sagdusmir/G32-Grill-Display-320x172-BT/misc/assembly/assembly_3_slide_pololu_down_the_case.jpeg

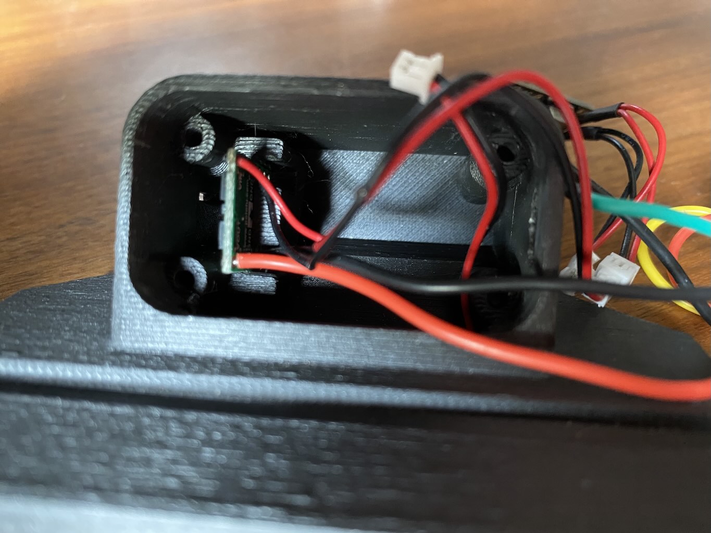
misc/assembly/assembly_3_slide_pololu_down_the_case.jpeg
