sagdusmir/G32-Grill-Display-320x172-BT/misc/assembly/assembly_4_orientation_of_the_charger_board.jpeg

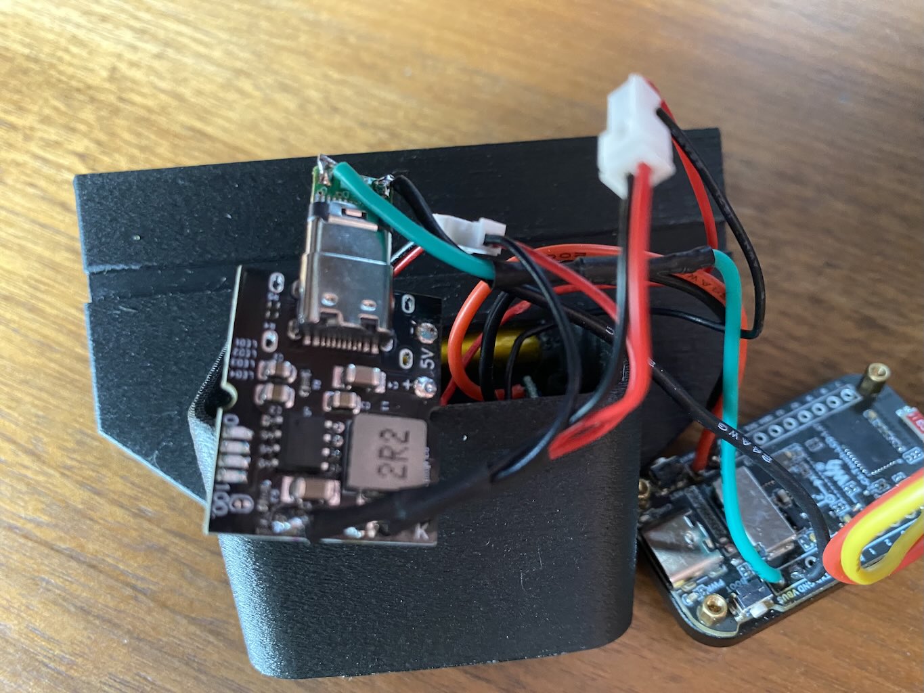
misc/assembly/assembly_4_orientation_of_the_charger_board.jpeg
