sagdusmir/G32-Grill-Display-320x172-BT/misc/assembly/assembly_5_push_charger_board_down_so_there_is_place_for_the_buzzer_on_top.jpeg

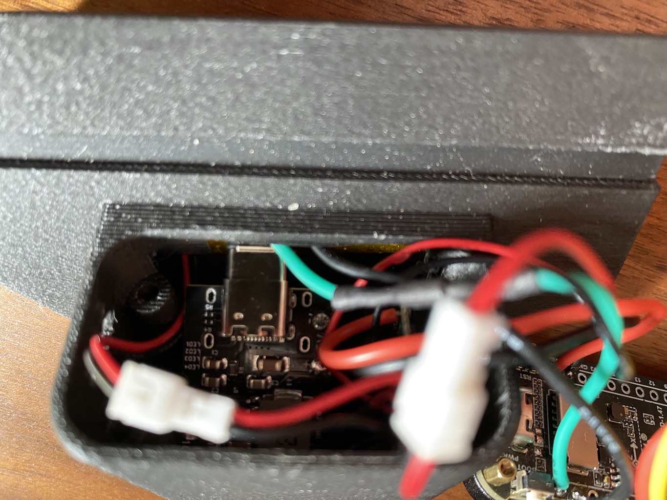
misc/assembly/assembly_5_push_charger_board_down_so_there_is_place_for_the_buzzer_on_top.jpeg
