sagdusmir/G32-Grill-Display-320x172-BT/misc/case/manual_tree_support_battery_cover.png

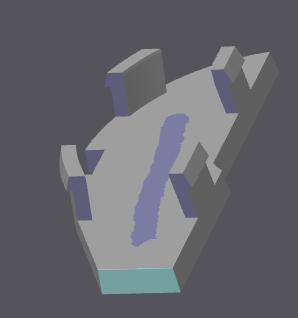
misc/case/manual_tree_support_battery_cover.png
